soynerdito/RickBadge/References/Scope/IMG_2160.JPG

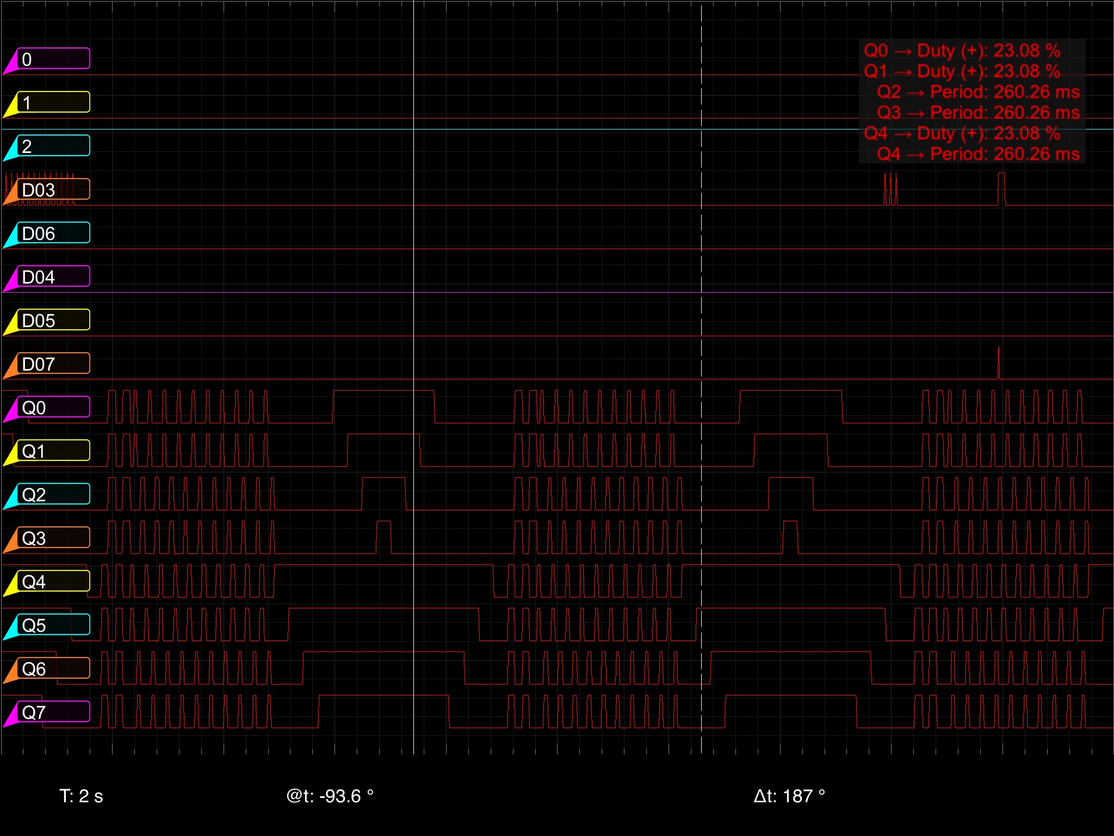
References/Scope/IMG_2160.JPG
