soynerdito/RickBadge/References/Scope/IMG_2161.JPG

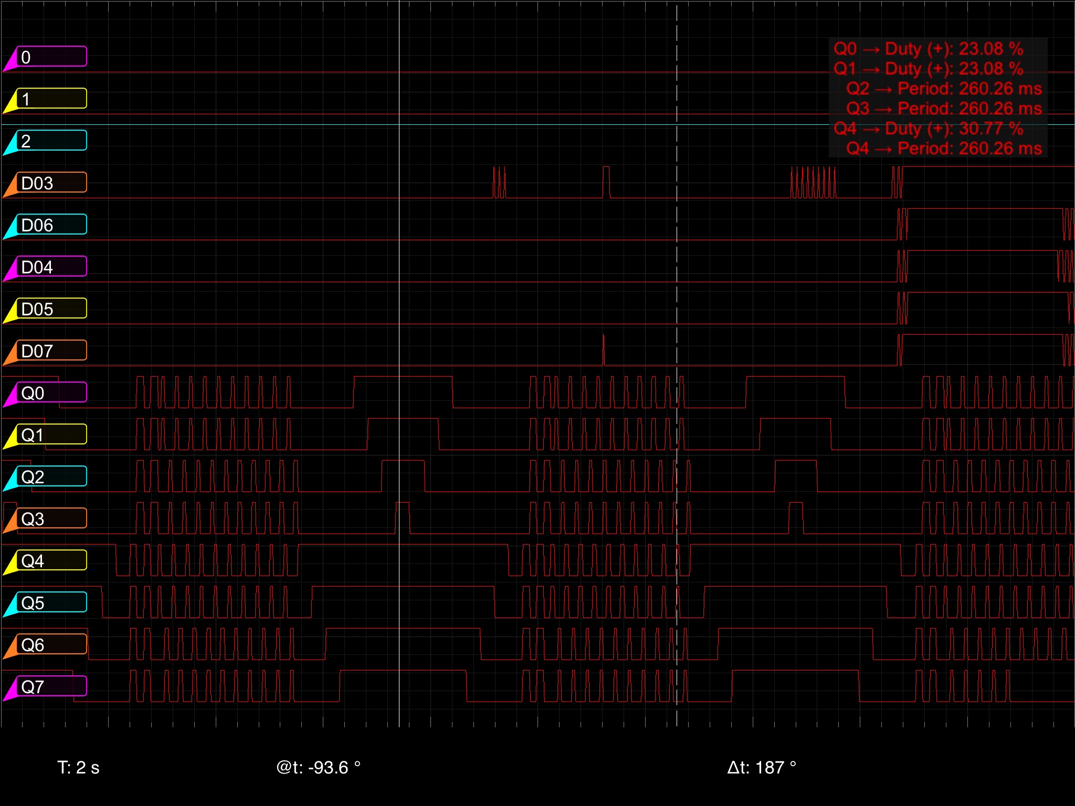
References/Scope/IMG_2161.JPG
