soynerdito/RickBadge/References/Scope/IMG_2162.JPG

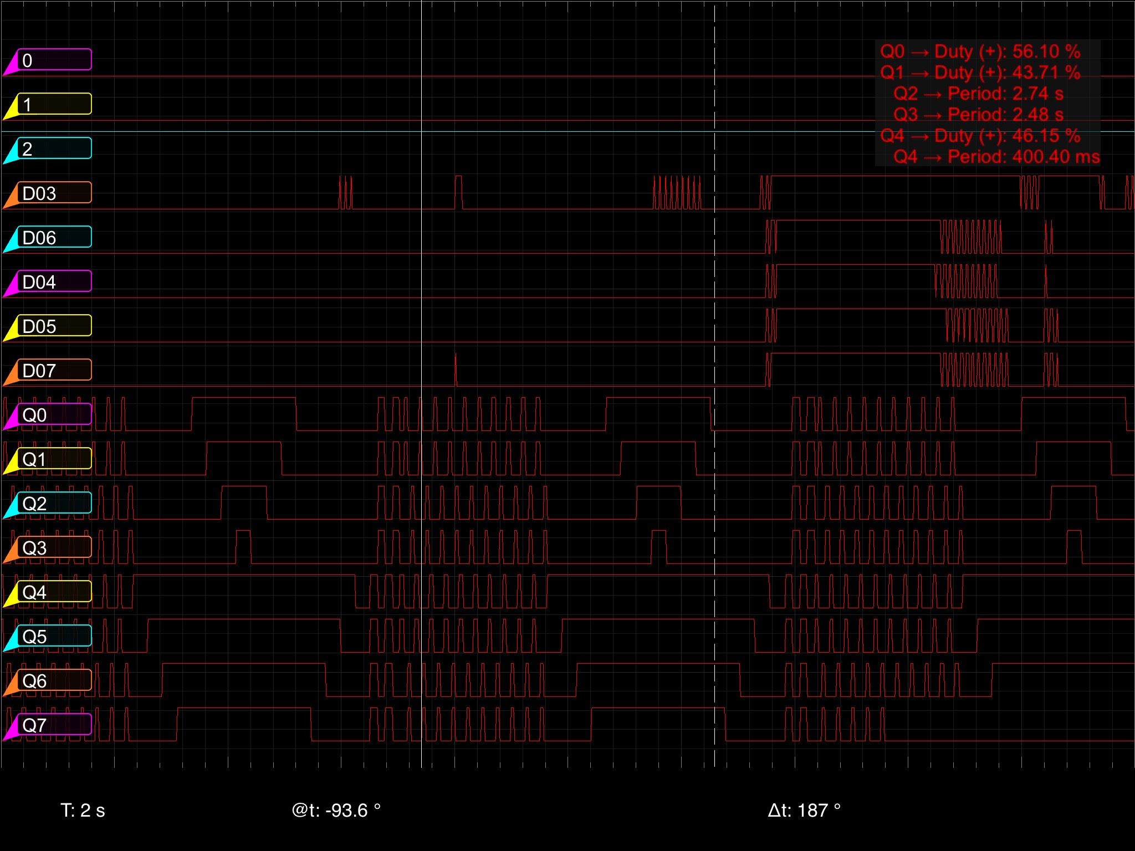
References/Scope/IMG_2162.JPG
