soynerdito/RickBadge/References/Scope/IMG_2163.JPG

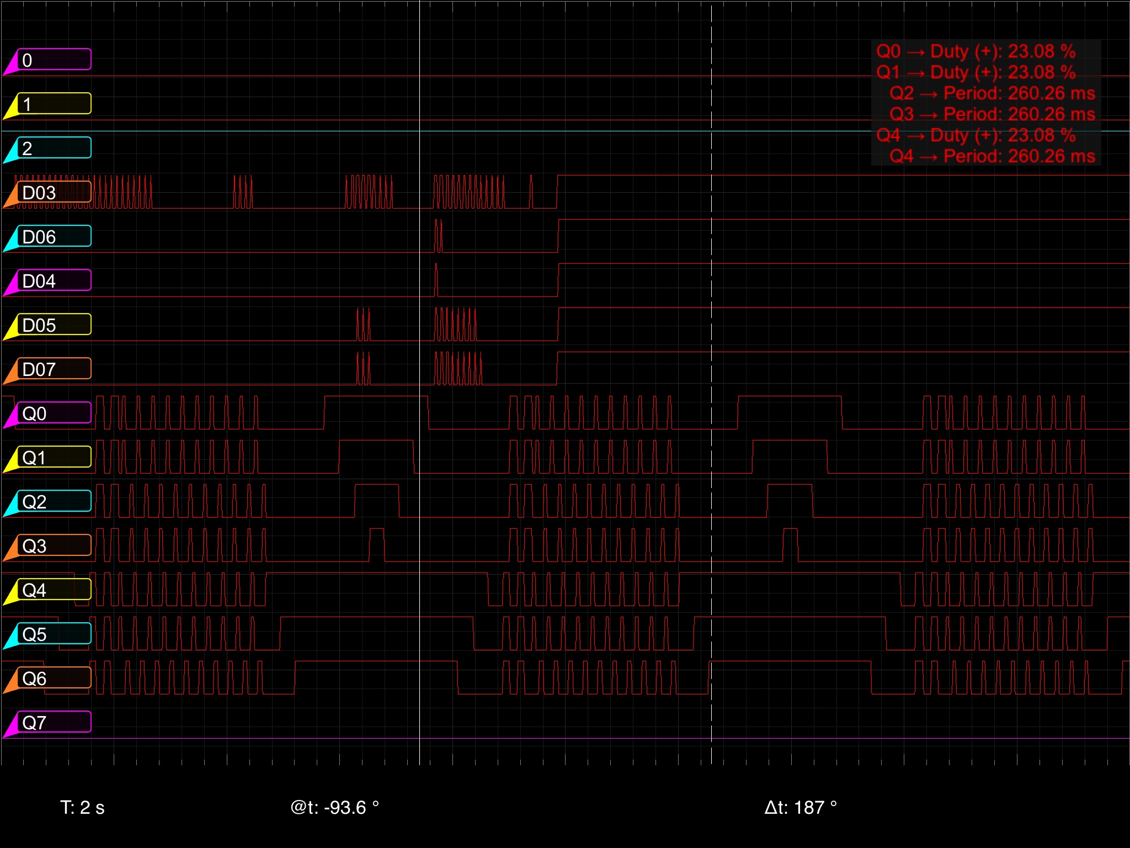
References/Scope/IMG_2163.JPG
