soynerdito/RickBadge/References/Scope/IMG_2164.JPG

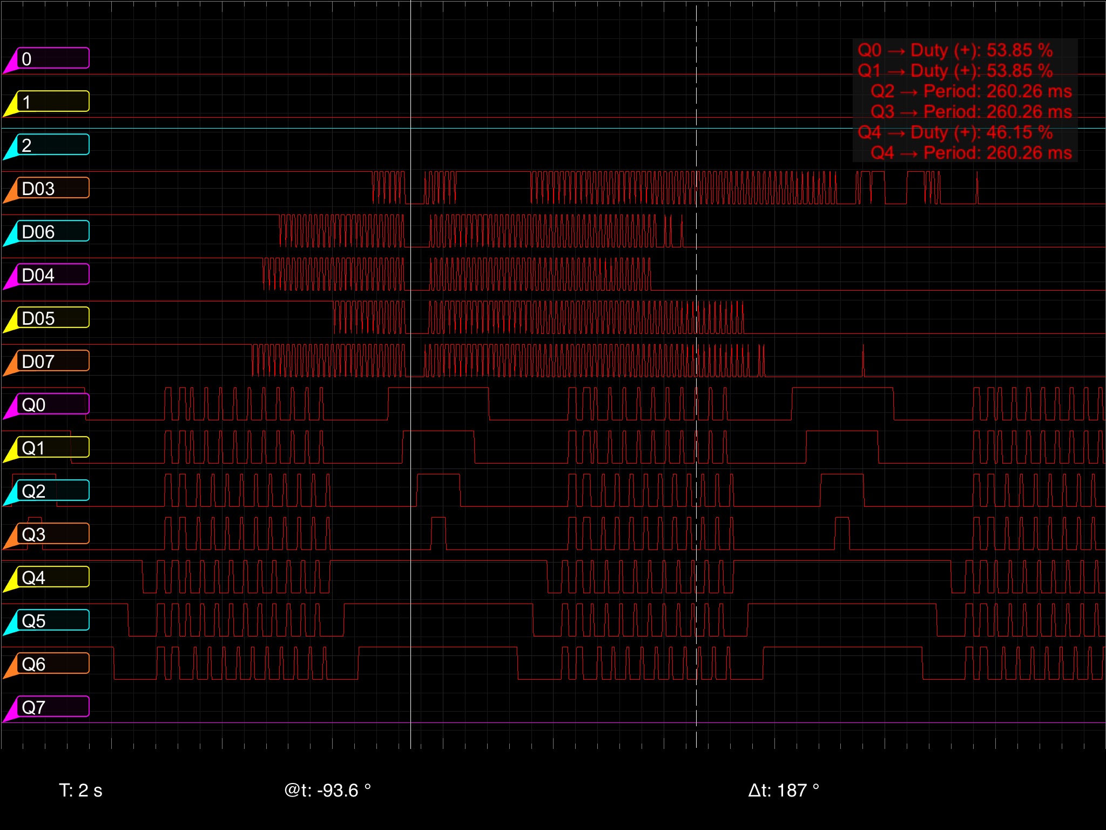
References/Scope/IMG_2164.JPG
