soynerdito/RickBadge/References/Scope/IMG_2165.JPG

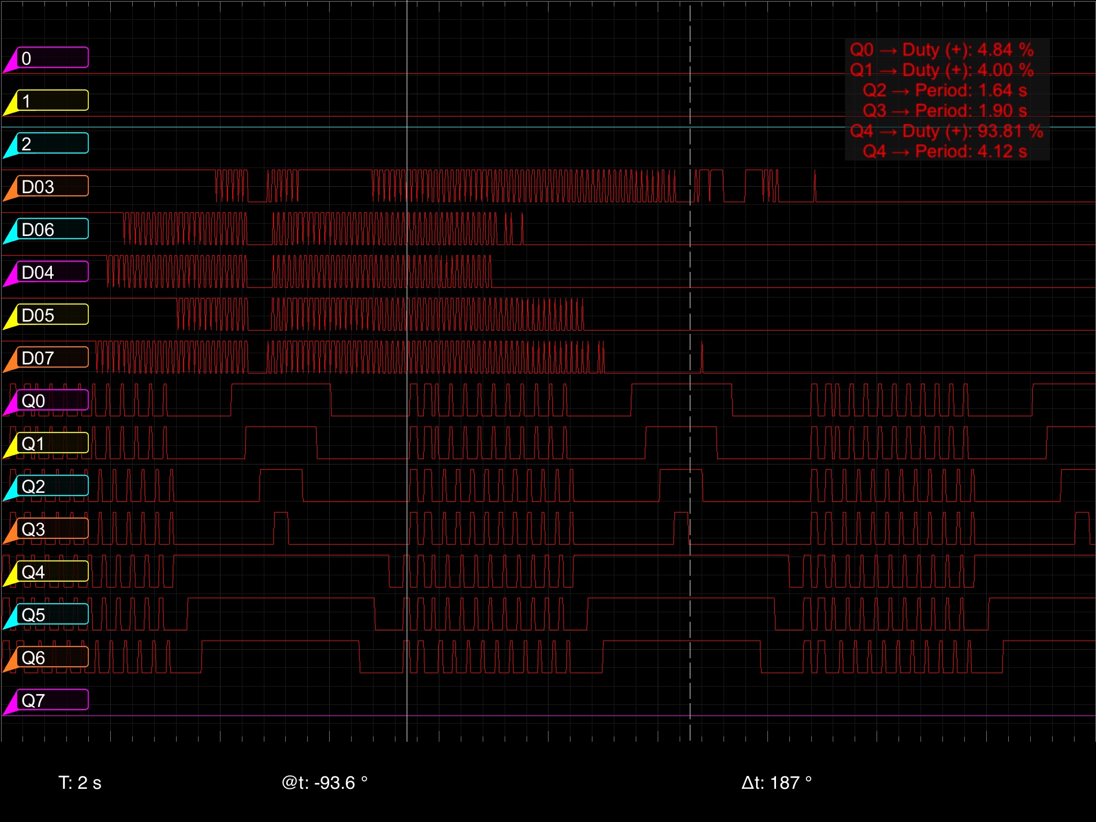
References/Scope/IMG_2165.JPG
