soynerdito/RickBadge/References/Scope/IMG_2166.JPG

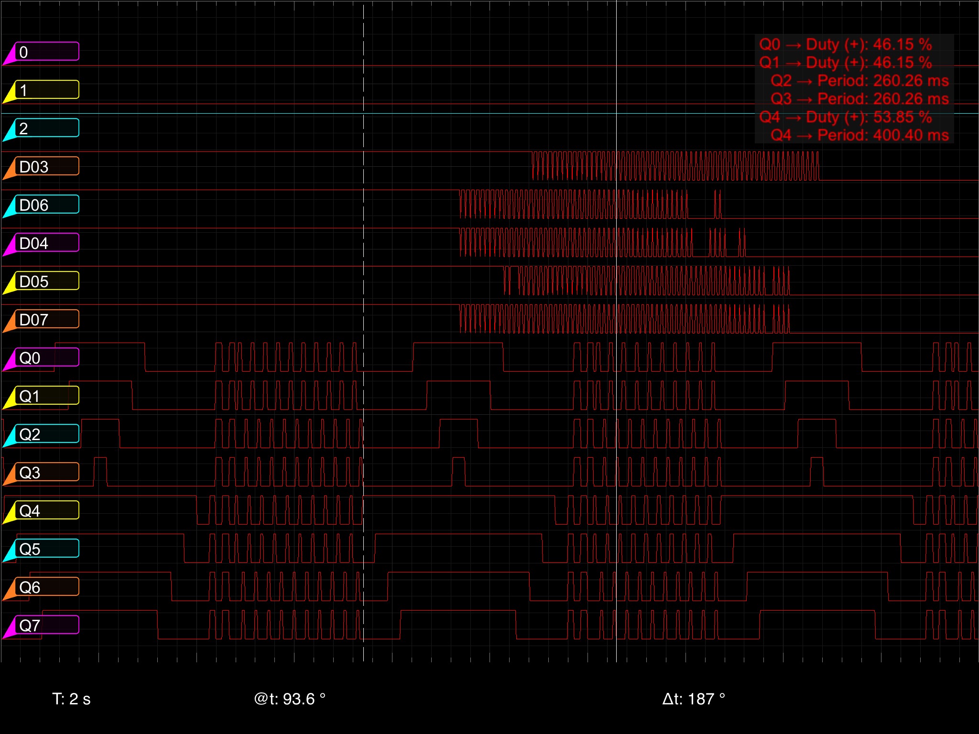
References/Scope/IMG_2166.JPG
